danielvilas/STM32-kicad-reference-designs/STM32F1/STM32F103/STM32F103CBT8_Devel/doc/pdf/STM32103_Devel-F_Mask.pdf

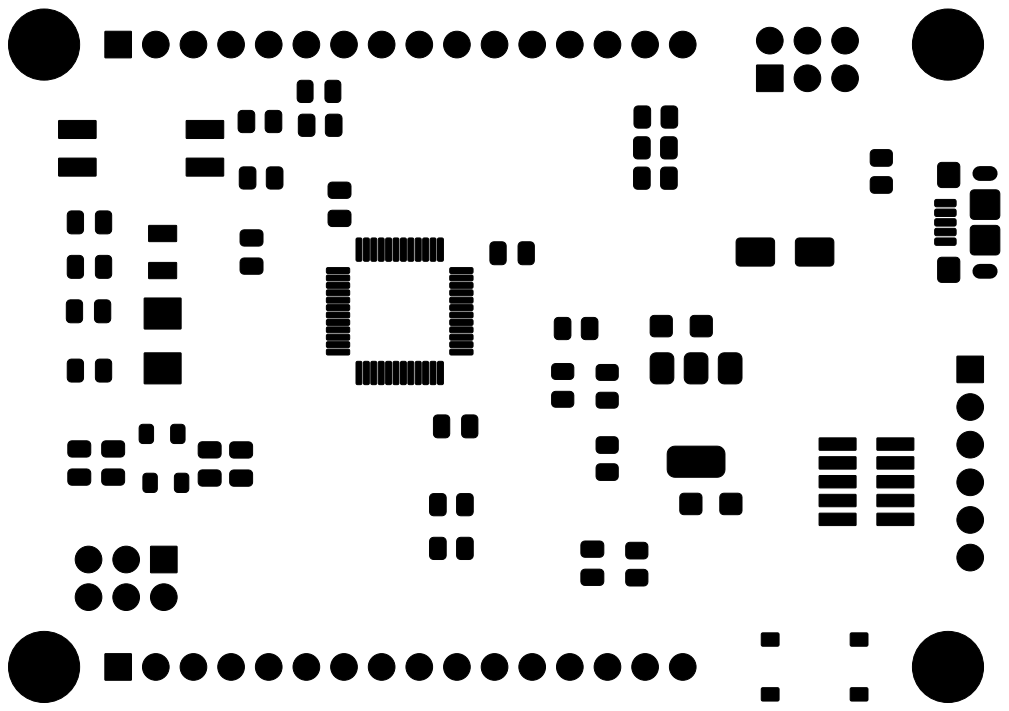
[picture p18: page 1]
