danielvilas/STM32-kicad-reference-designs/STM32F1/STM32F103/STM32F103CBT8_Devel/doc/pdf/STM32103_Devel-F_Paste.pdf

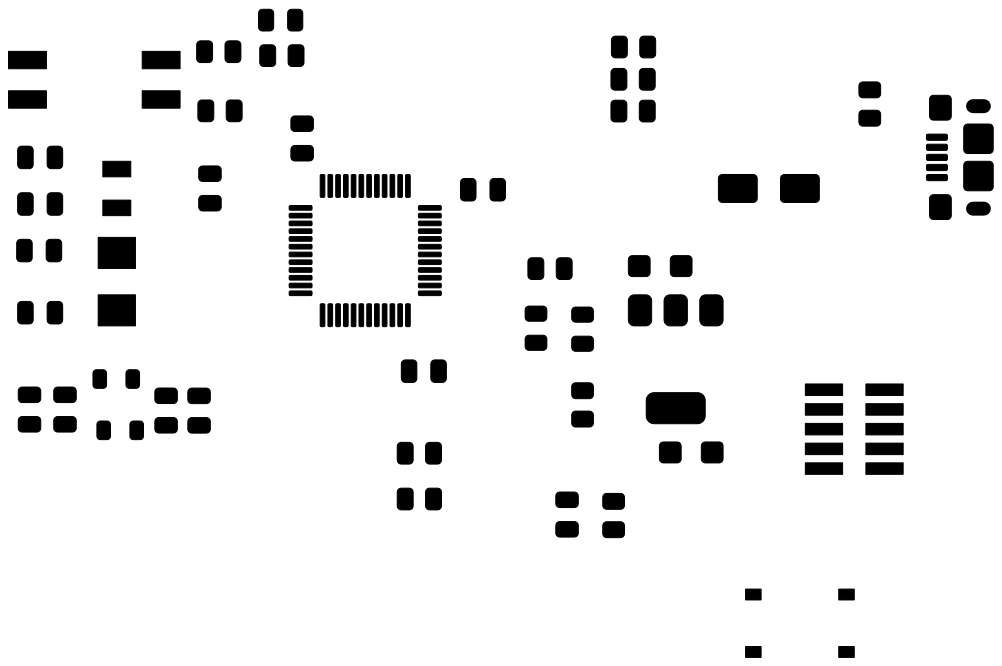
[picture p19: page 1]
