danielvilas/STM32-kicad-reference-designs/STM32F0/STM32F030/STM32F030K6T6TR_Devel/doc/pdf/STM32F030K6T6TR_Devel-B_Mask.pdf

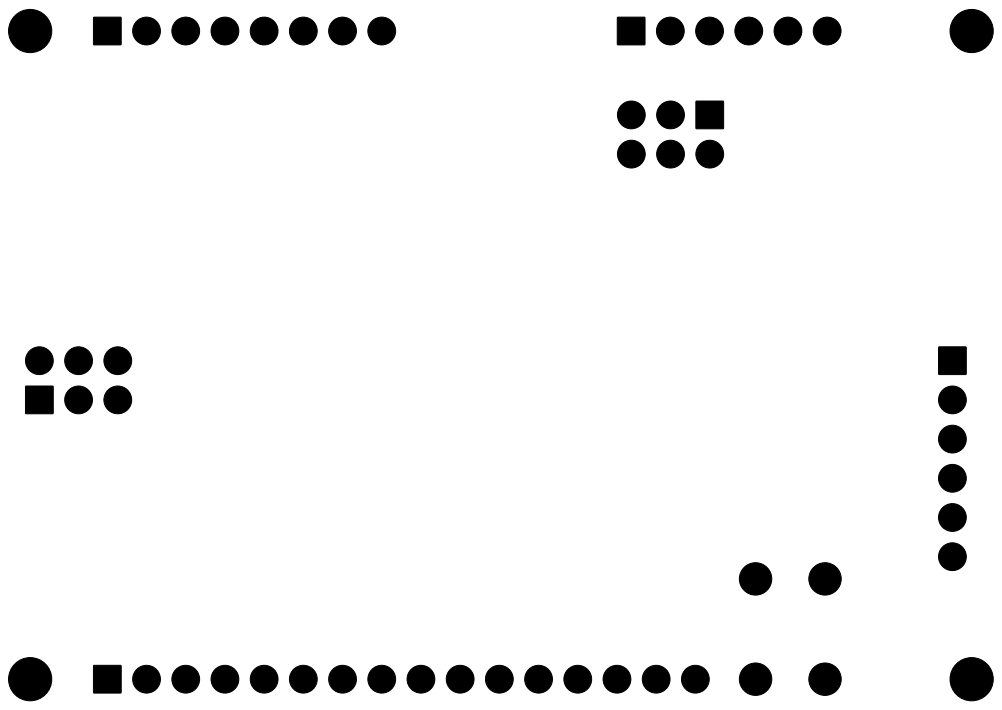
[picture p25: page 1]
