danielvilas/STM32-kicad-reference-designs/STM32F0/STM32F030/STM32F030K6T6TR_Devel/doc/pdf/STM32F030K6T6TR_Devel-F_Cu.pdf

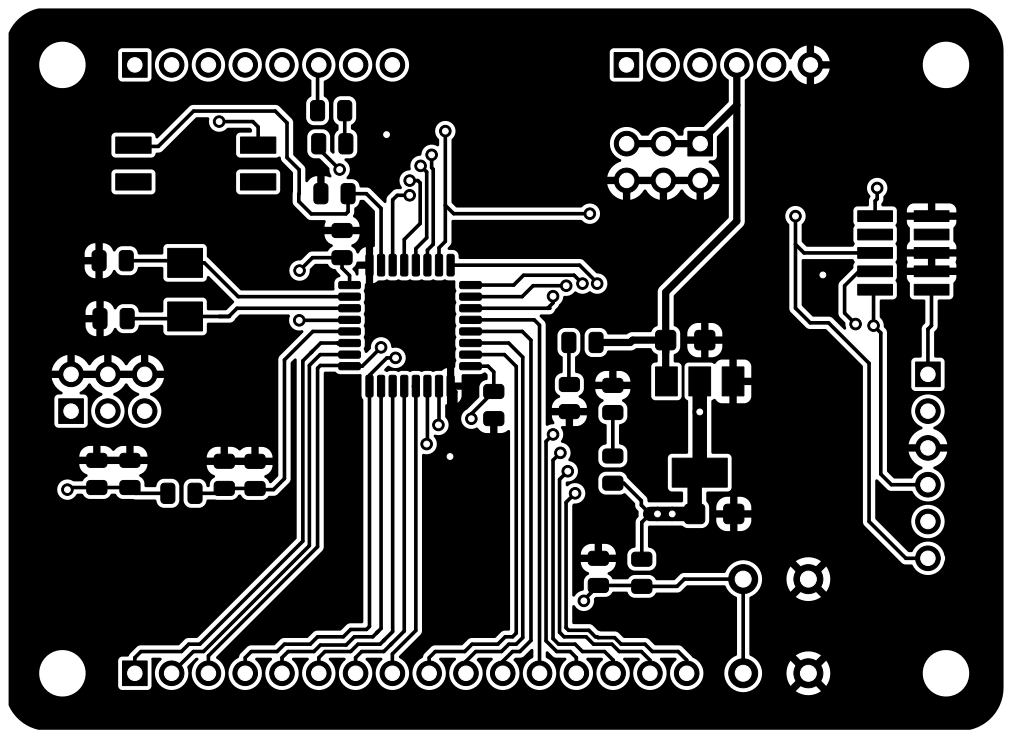
[picture p27: page 1]
