danielvilas/STM32-kicad-reference-designs/STM32F0/STM32F030/STM32F030K6T6TR_Devel/doc/pdf/STM32F030K6T6TR_Devel-F_Fab.pdf

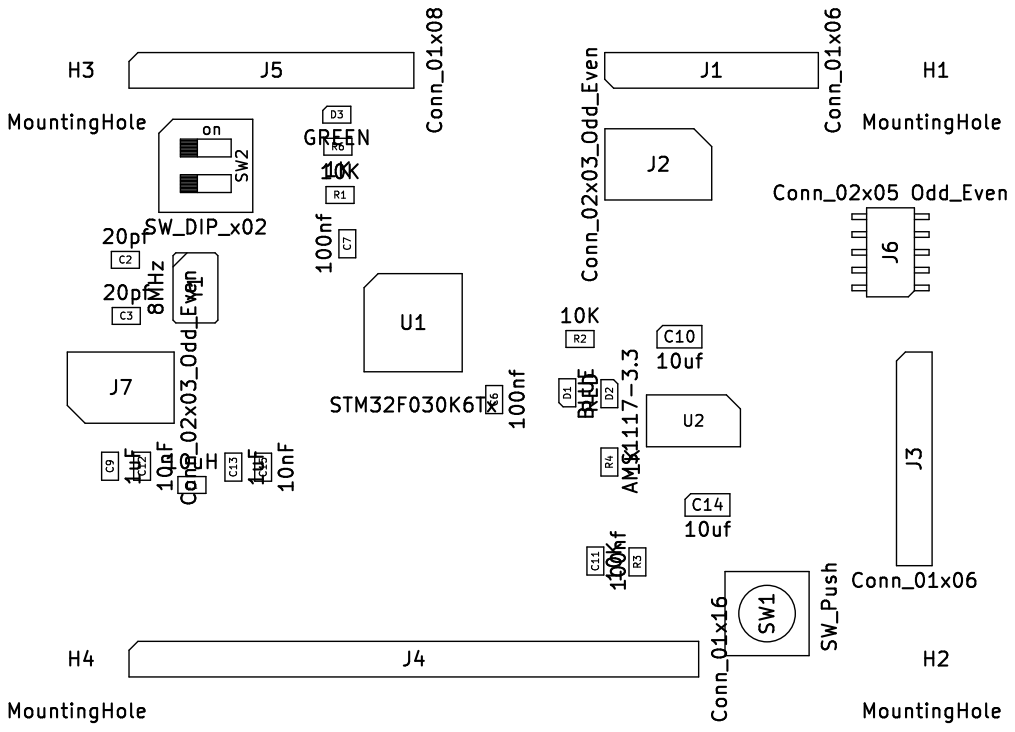
[picture p28: page 1]
