danielvilas/STM32-kicad-reference-designs/STM32F0/PlatformIo/variant_STM32F030K6T6TR_DEVEL_V0.cpp

/*
 *******************************************************************************
 * Copyright (c) 2020-2021, STMicroelectronics
 * All rights reserved.
 *
 * This software component is licensed by ST under BSD 3-Clause license,
 * the "License"; You may not use this file except in compliance with the
 * License. You may obtain a copy of the License at:
 *                        opensource.org/licenses/BSD-3-Clause
 *
 *******************************************************************************
 */
#if defined(ARDUINO_STM32F030K6T6TR_DEVEL_V0)
#include "pins_arduino.h"

// Digital PinName array
const PinName digitalPin[] = {
  PA_0,   // D1/A0
  PA_1,   // D2/A1
  PA_2,   // D3/A2
  PA_3,   // D4/A3
  PA_4,   // D5/A4
  PA_5,   // D6/A5
  PA_6,   // D7/A6
  PA_7,   // D8/A7
  PA_8,   // D9
  PA_9,   // D10
  PA_10,  // D11
  PA_11,  // D12
  PA_12,  // D13
  PA_13,  // D14
  PA_14,  // D15
  PA_15,  // D16
  PB_0,   // D17/A8
  PB_1,   // D18/A9
  PB_3,   // D19
  PB_4,   // D20
  PB_5,   // D21
  PB_6,   // D22
  PB_7,   // D23
  PF_0,   // D24
  PF_1    // D25
};

// Analog (Ax) pin number array
const uint32_t analogInputPin[] = {
  0,  // A0,  PA0
  1,  // A1,  PA1
  2,  // A2,  PA2
  3,  // A3,  PA3
  4,  // A4,  PA4
  5,  // A5,  PA5
  6,  // A6,  PA6
  7,  // A7,  PA7
  16, // A8,  PB0
  17  // A9,  PB1
};


extern "C"{
  /**
    * @brief  System Clock Configuration
    * @param  None
    * @retval None
    */
  WEAK void SystemClock_Config(void)
  {
    RCC_OscInitTypeDef RCC_OscInitStruct = {0};
    RCC_ClkInitTypeDef RCC_ClkInitStruct = {0};
    RCC_PeriphCLKInitTypeDef PeriphClkInit = {0};

    /** Initializes the RCC Oscillators according to the specified parameters
    * in the RCC_OscInitTypeDef structure.
    */
    RCC_OscInitStruct.OscillatorType = RCC_OSCILLATORTYPE_HSE;
    RCC_OscInitStruct.HSEState = RCC_HSE_ON;
    RCC_OscInitStruct.PLL.PLLState = RCC_PLL_ON;
    RCC_OscInitStruct.PLL.PLLSource = RCC_PLLSOURCE_HSE;
    RCC_OscInitStruct.PLL.PLLMUL = RCC_PLL_MUL6;
    RCC_OscInitStruct.PLL.PREDIV = RCC_PREDIV_DIV1;
    if (HAL_RCC_OscConfig(&RCC_OscInitStruct) != HAL_OK)
    {
      Error_Handler();
    }
    /** Initializes the CPU, AHB and APB buses clocks
    */
    RCC_ClkInitStruct.ClockType = RCC_CLOCKTYPE_HCLK|RCC_CLOCKTYPE_SYSCLK
                                |RCC_CLOCKTYPE_PCLK1;
    RCC_ClkInitStruct.SYSCLKSource = RCC_SYSCLKSOURCE_PLLCLK;
    RCC_ClkInitStruct.AHBCLKDivider = RCC_SYSCLK_DIV1;
    RCC_ClkInitStruct.APB1CLKDivider = RCC_HCLK_DIV1;

    if (HAL_RCC_ClockConfig(&RCC_ClkInitStruct, FLASH_LATENCY_1) != HAL_OK)
    {
      Error_Handler();
    }
  PeriphClkInit.PeriphClockSelection = RCC_PERIPHCLK_USART1 | RCC_PERIPHCLK_I2C1;
  PeriphClkInit.Usart1ClockSelection = RCC_USART1CLKSOURCE_PCLK1;
  PeriphClkInit.I2c1ClockSelection = RCC_I2C1CLKSOURCE_SYSCLK;
    if (HAL_RCCEx_PeriphCLKConfig(&PeriphClkInit) != HAL_OK)
    {
      Error_Handler();
    }
  }


}

#endif /* ARDUINO_GENERIC_* */
